T-McBride/Abby_Mirror/images/Internals.jpg

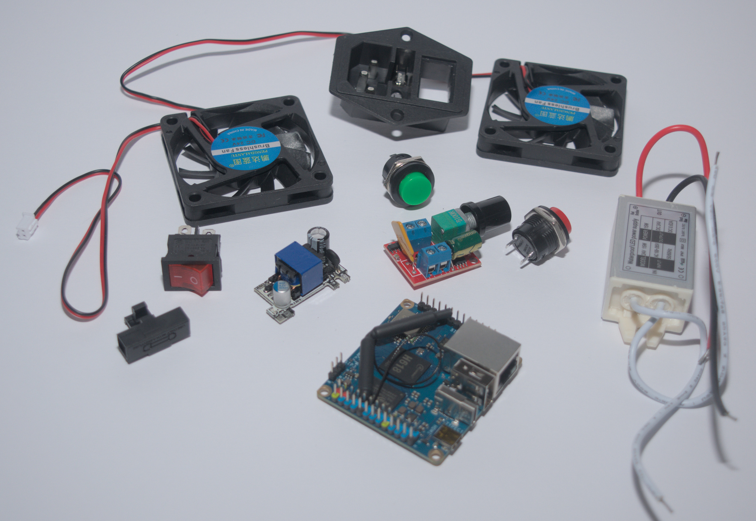
images/Internals.jpg
